IRandonation/keyboard/Rock_Number_keyboard/3D/定位板.SLDPRT

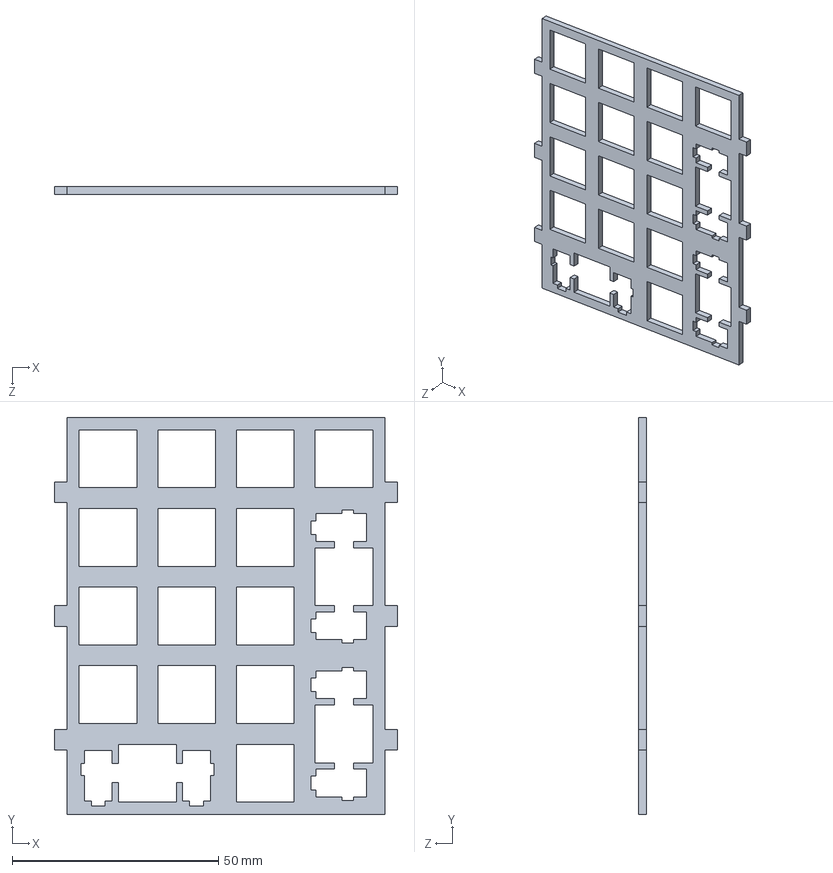
[picture p12: CAD file, 2025-02-01]
Rock_Number_keyboard/3D/定位板.SLDPRT
83.1 x 96.2 x 2.00 mm
