IRandonation/keyboard/Rock_Number_keyboard/3D/键盘.STEP

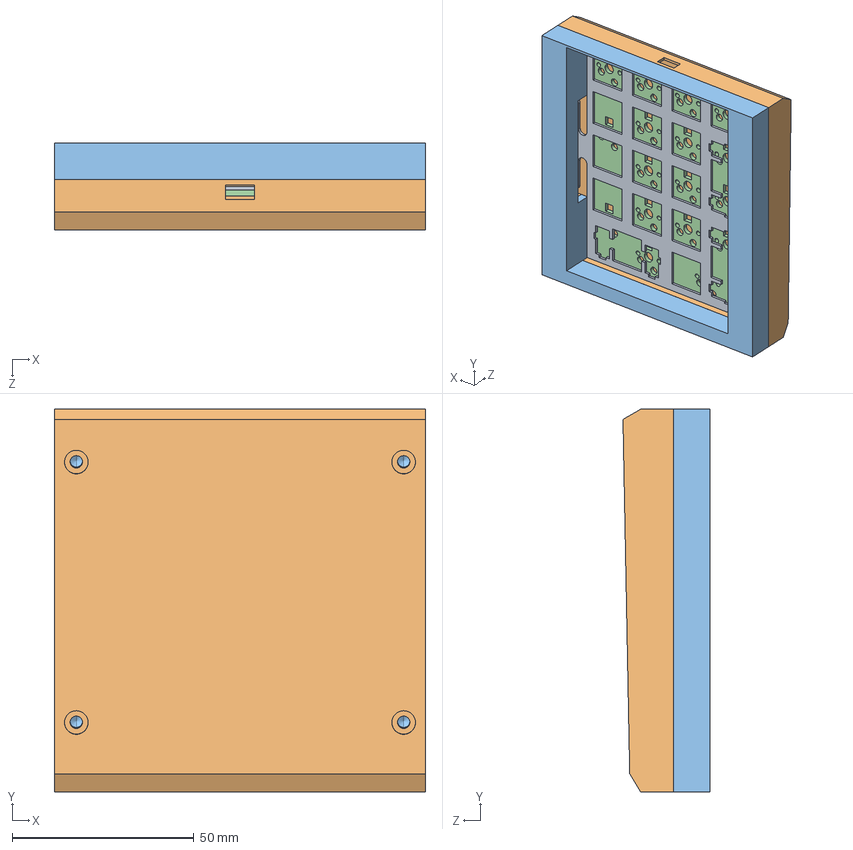
[picture p13: CAD file, 2025-02-01]
Rock_Number_keyboard/3D/键盘.STEP
102.0 x 105.3 x 23.9 mm
定位板
外壳
外壳-2
Board
